MineaEdi/SI_Car/schematics/pico_w_pinout/pico_w_pinout.kicad_sch

## KiCad design schematics/pico_w_pinout/pico_w_pinout.kicad_sch (2025-01-12)

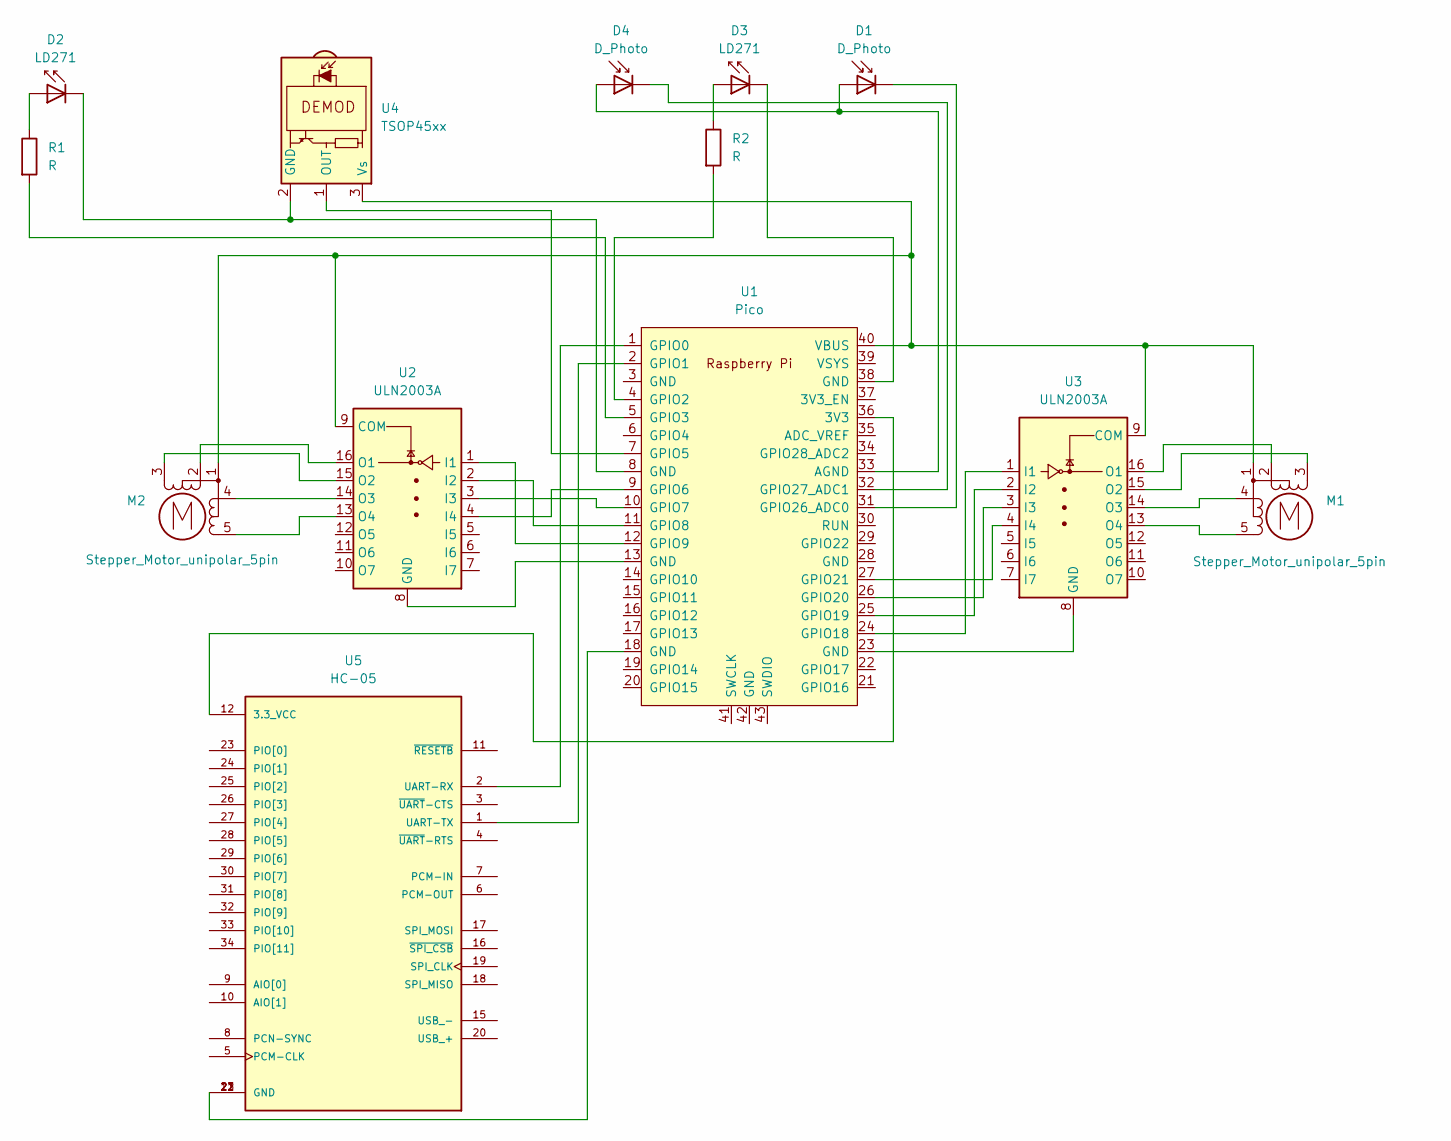
[picture p9: schematic pico_w_pinout.kicad_sch]

Parts:
D1, D4: D_Photo
D2, D3: LD271; LED_D5.0mm_IRGrey
M1, M2: Stepper_Motor_unipolar_5pin
R1, R2: R
U1: Pico; RPi_Pico_SMD_TH
U2, U3: ULN2003A
U4: TSOP45xx; Vishay_MOLD-3Pin
U5: HC-05; XCVR_HC-05; PARTREV v1.0

Connections:
unnamed: D1.1 (K), U1.31 (GPIO26_ADC0)
unnamed: D1.2 (A), D4.2 (A), U1.33 (AGND)
unnamed: D2.1 (K), U1.8 (GND), U4.2 (GND)
unnamed: D2.2 (A), R1.1
unnamed: D3.1 (K), U1.38 (GND)
unnamed: D3.2 (A), R2.1
unnamed: D4.1 (K), U1.32 (GPIO27_ADC1)
unnamed: M1.1, M2.1, U1.40 (VBUS), U2.9 (COM), U3.9 (COM), U4.3 (Vs)
unnamed: M1.2, U3.16 (O1)
unnamed: M1.3 (-), U3.15 (O2)
unnamed: M1.4, U3.14 (O3)
unnamed: M1.5, U3.13 (O4)
unnamed: M2.2, U2.16 (O1)
unnamed: M2.3 (-), U2.15 (O2)
unnamed: M2.4, U2.14 (O3)
unnamed: M2.5, U2.13 (O4)
unnamed: R1.2, U1.5 (GPIO3)
unnamed: R2.2, U1.4 (GPIO2)
unnamed: U1.1 (GPIO0), U5.2 (UART-RX)
unnamed: U1.2 (GPIO1), U5.1 (UART-TX)
unnamed: U1.7 (GPIO5), U4.1 (OUT)
unnamed: U1.9 (GPIO6), U2.4 (I4)
unnamed: U1.10 (GPIO7), U2.3 (I3)
unnamed: U1.11 (GPIO8), U2.2 (I2)
unnamed: U1.12 (GPIO9), U2.1 (I1)
unnamed: U1.13 (GND), U2.8 (GND)
unnamed: U1.18 (GND), U5.13 (GND), U5.21 (GND), U5.22 (GND)
unnamed: U1.23 (GND), U3.8 (GND)
unnamed: U1.24 (GPIO18), U3.1 (I1)
unnamed: U1.25 (GPIO19), U3.2 (I2)
unnamed: U1.26 (GPIO20), U3.3 (I3)
unnamed: U1.27 (GPIO21), U3.4 (I4)
unnamed: U1.36 (3V3), U5.12 (3.3_VCC)
